stb49078/nscale-adapter-decoder/loc-decoder/Roco/1044/NEM-651_Adapter/schematic.png

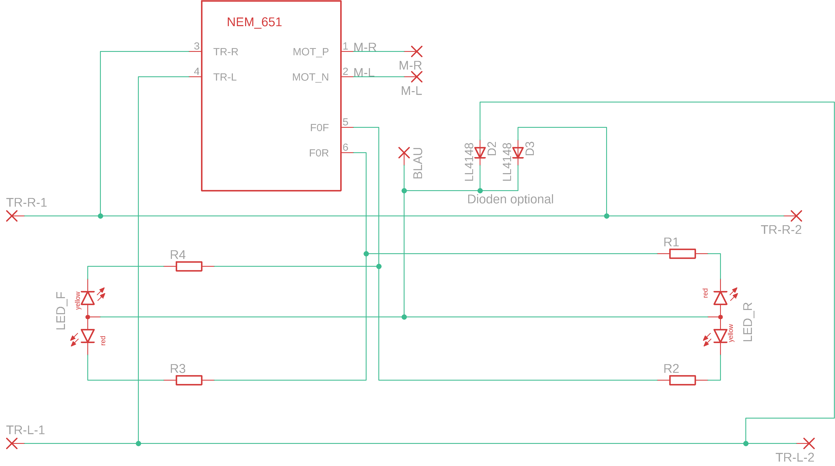
loc-decoder/Roco/1044/NEM-651_Adapter/schematic.png
