stb49078/nscale-adapter-decoder/loc-decoder/Spectrum/GE_Dash_8-40CW/Decoder-BD62xx-Railcom/schematic.png

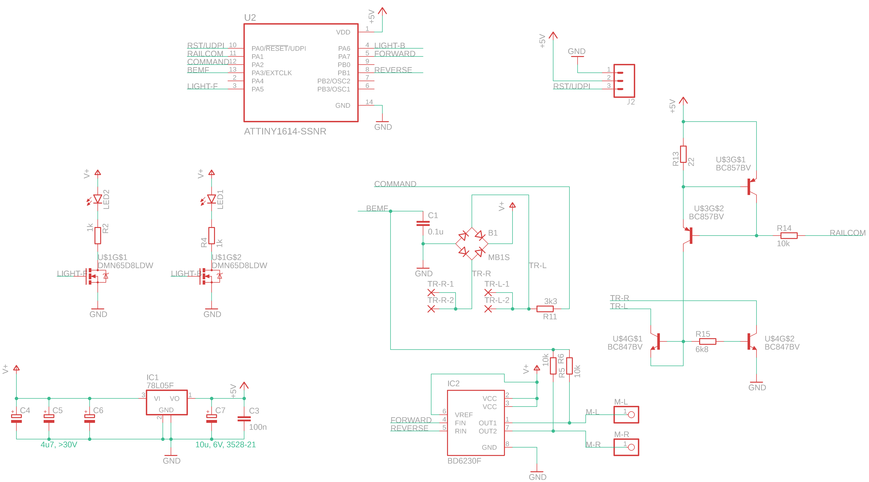
loc-decoder/Spectrum/GE_Dash_8-40CW/Decoder-BD62xx-Railcom/schematic.png
