stb49078/nscale-adapter-decoder/scans/Epson_0634_1.png

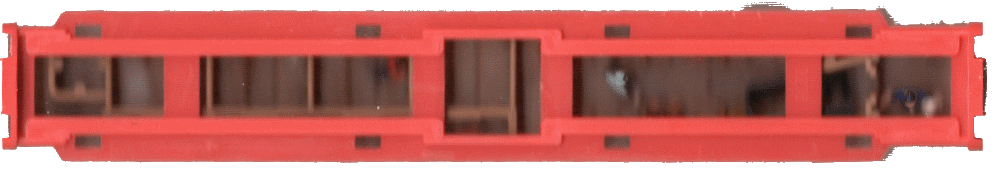
scans/Epson_0634_1.png
