stb49078/nscale-adapter-decoder/wagon-light/Minitrix/Eurofima/schematic.png

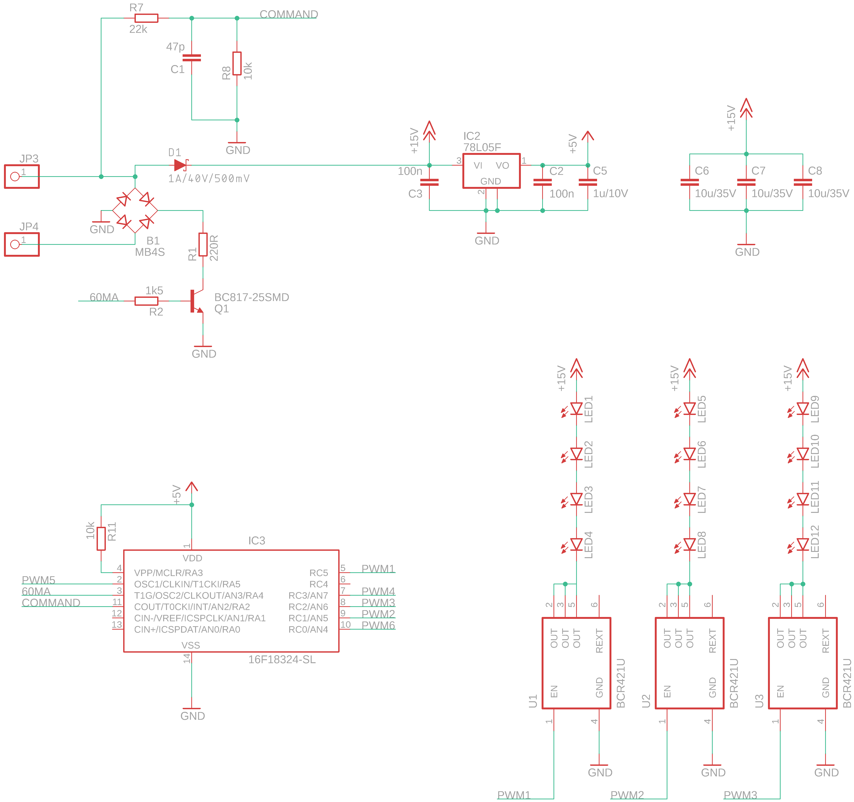
wagon-light/Minitrix/Eurofima/schematic.png
