stb49078/nscale-adapter-decoder/wagon-light/Roco/Eilzugwagen/schematic.png

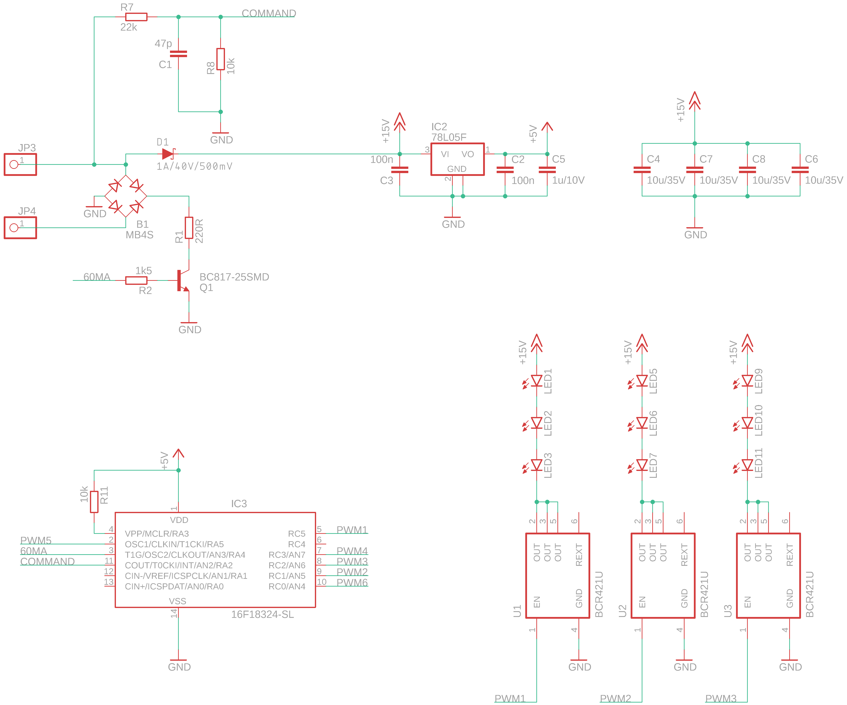
wagon-light/Roco/Eilzugwagen/schematic.png
